mureytasroc/trintheremin-public/Circuit_Design/Design Pictures/Schematic/SchematicFull.jpg

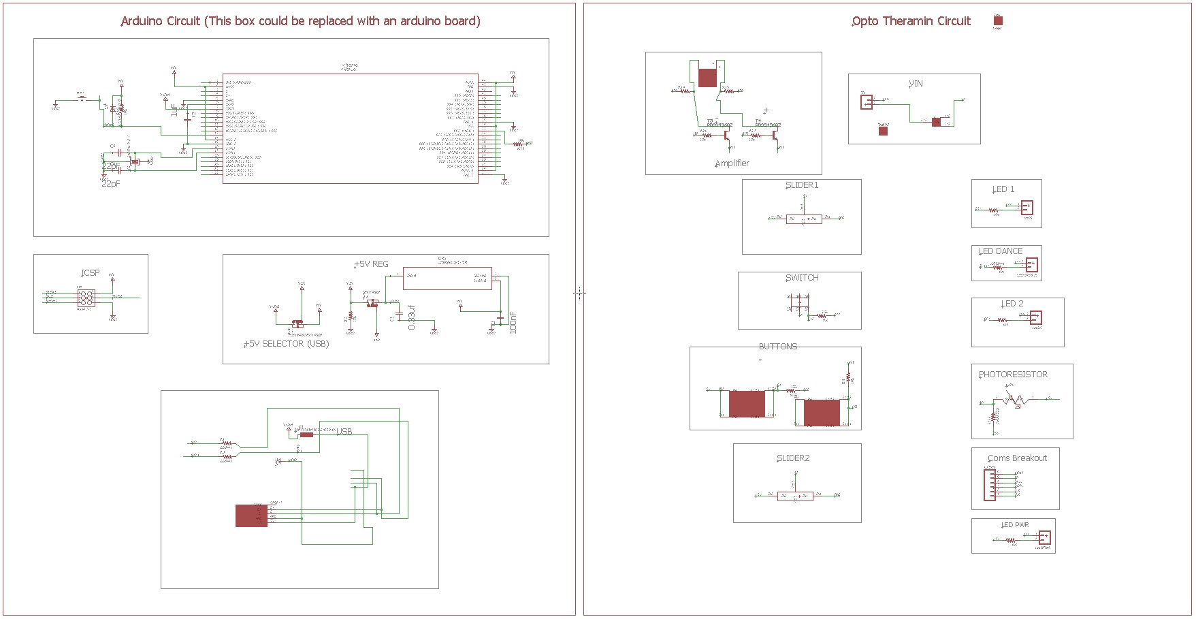
Circuit_Design/Design Pictures/Schematic/SchematicFull.jpg
