mureytasroc/trintheremin-public/TrinTheremin Resources/Circuit Design/TrinTheremin.sch

## EAGLE design TrinTheremin Resources/Circuit Design/TrinTheremin.sch (2017-09-11)


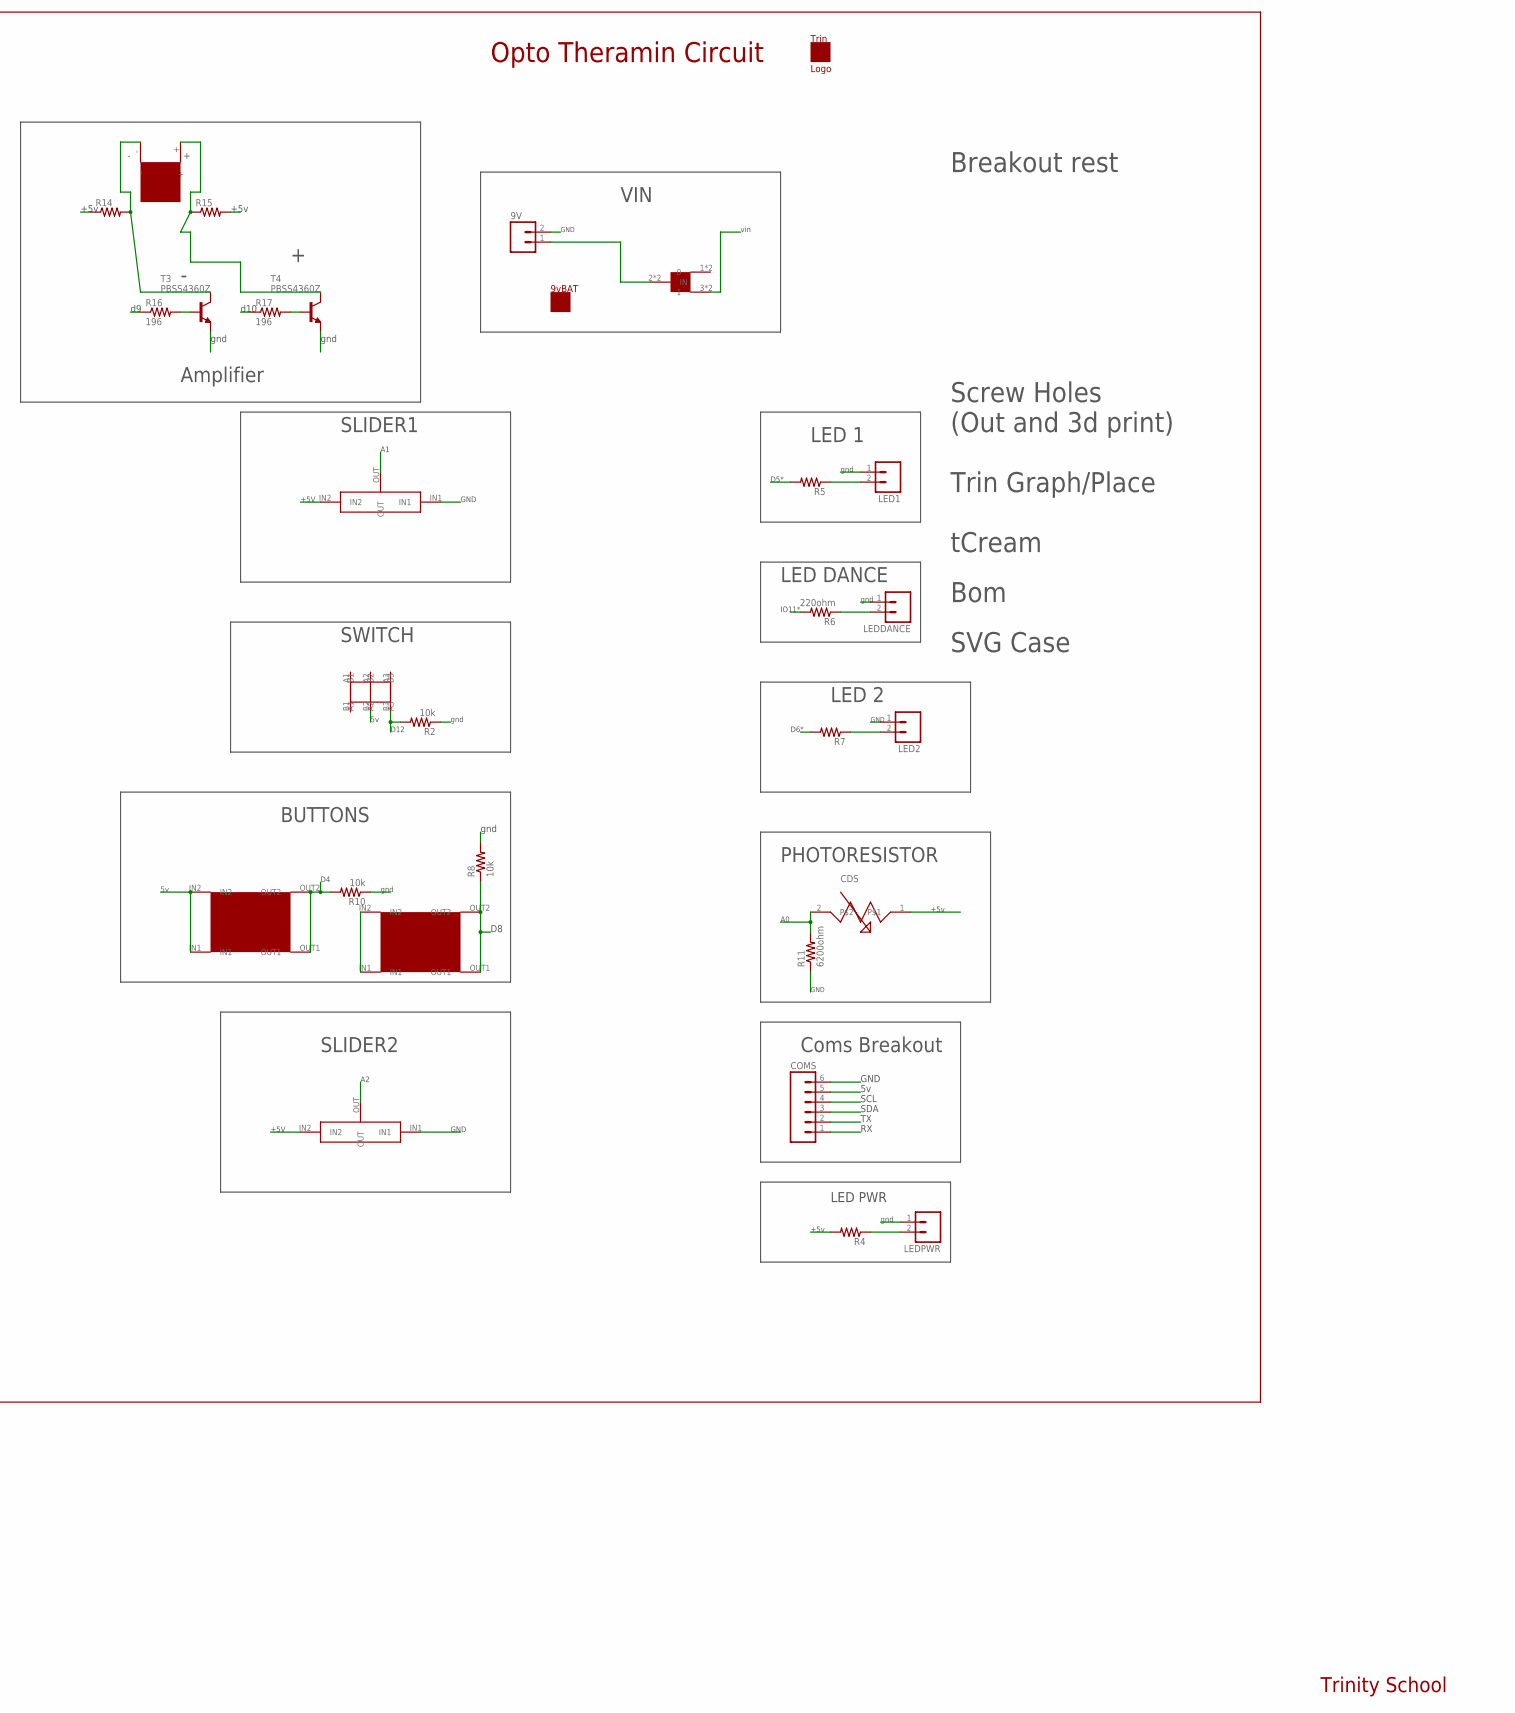
[picture p22: schematic TrinTheremin.sch, part in row 1, column 2]

Parts:
9V: M02PTH; 1X02
C1: 0.33uf; CAPC2013X110N
C2: 100nF; CAPC2013X110N
C3: 1uF; CAPC1608X85N
C4, C5: 22pF; CAPC1608X85N
COMS: M06SILK_FEMALE_PTH; 1X06
CR1: L7805CDT-TR; DPAK
D1: CD1206-S01575; MINIMELF
F1: MF-MSMF050-2 500mA; L1812
ICSP: FEMALE 2x3; 2X3
LED1, LED2: M02PTH; 1X02
LEDDANCE: M02PTH; 1X02
LEDPWR: M02PTH; 1X02
R1, R3: 22ohm; R0603
R2, R8, R9, R10, R12, R13: 10k; 0603-RES
R4, R5, R7: RESISTOR0603; 0603-RES
R6: 220ohm; 0603-RES
R11: 6200ohm; 0603-RES
R14, R15: R-US_R2512; R2512
R16, R17: 196; 1206
RESET: SWITCH_PUSHBUTTONC&K_KSS; BTN_CK_KSS
T1: FDN340P/PMV48XP; SOT-23
T2: PMV48XP; SOT-23
T3, T4: PBSS4360Z; SOT223
U$3: ATMEGA32U4-AU; 44ML
U$8: PWRSWITCHTHRU
U$9: CDS
U$10, U$14: DIGISLIDER
U$11: DIGISWITCH
U$13, U$17: BUT97
U$15: 9VBATHOLDERTALL
U$16: TRIN
U$20: GOODSPEAKER
U$23: MICROUSB
Y2: 16MHz KX-7; CRYSTAL-3.2-2.5

Connections:
+5V: C2.2 (C2), COMS.5, CR1.2 (OUTPUT), D1.C, ICSP.2, R4.2, R12.2, R14.1, R15.2, T1.2 (S), T2.3 (G), U$3.2 (UVCC), U$3.14 (VCC_2), U$3.24 (AVCC_2), U$3.34 (VCC), U$3.44 (AVCC), U$9.1, U$10.IN2, U$11.B2, U$13.IN1, U$13.IN2, U$14.IN2, U$17.IN1, U$17.IN2
+VIN: C1.2 (C2), CR1.1 (INPUT), T2.2 (S)
A0: R11.2, U$3.36 (PF7_(ADC7/TDI)), U$9.2
A1: U$3.37 (PF6_(ADC6/TDO)), U$10.OUT
A2: U$3.38 (PF5_(ADC5/TMS)), U$14.OUT
A3: U$3.39 (PF4_(ADC4/TCK))
A4: U$3.40 (PF1_(ADC1))
A5: U$3.41 (PF0_(ADC0))
BASE: R16.2, T3.1 (B)
COL: R14.2, T3.2 (C), U$20.-
D0/RX: COMS.1, U$3.20 ((RXD1/INT2)_PD2)
D1/TX: COMS.2, U$3.21 ((TXD1/INT3)_PD3)
D2/SDA: COMS.3, U$3.19 ((SDA/INT1)_PD1)
D3/SCL: COMS.4, U$3.18 ((OC0B/SCL/INT0)_PD0)
D4*: R10.2, U$3.25 (PD4_(ICP1/ADC8), U$13.OUT1, U$13.OUT2
D5*: R5.2, U$3.31 (PC6_(OC3A/OC4A!))
D6*: R7.2, U$3.27 (PD7_(T0/OC4D/ADC10))
D7: U$3.1 (INT.6/AIN0)PE6)
D+: R3.2, U$23.D+
D-: R1.2, U$23.D-
GND: 9V.2, C1.1 (C1), C2.1 (C1), C3.2 (C2), C4.1 (C1), C5.1 (C1), COMS.6, CR1.3 (GROUND), ICSP.6, LED1.1, LED2.1, LEDDANCE.1, LEDPWR.1, R2.1, R8.2, R9.1, R10.1, R11.1, R13.1, RESET.P$1, T3.3 (E), T4.3 (E), U$3.5 (UGND), U$3.15 (GND_2), U$3.23 (GND_3), U$3.35 (GND_4), U$3.43 (GND), U$10.IN1, U$14.IN1, U$23.GND, Y2.2 (GND), Y2.4 (GND)
HWB: R13.2, U$3.33 (PE2_(HWB!))
IO8: R8.1, U$3.28 (PB4_(PCINT4/ADC11)), U$17.OUT1, U$17.OUT2
IO9*: R16.1, U$3.29 (PB5_(PCINT5/OC1A/OC4B/ADC12))
IO10*: R17.1, U$3.30 (PB6_(PCINT6/OC1B/OC4B/ADC13))
IO11*: R6.2, U$3.12 ((PCINT7/OC0A/OC1C/RTS!)_PB7)
IO12*: R2.2, U$3.26 (PD6_(T1/OC4D/ADC9)), U$11.B3
IO13*: U$3.32 (PC7_(ICP3/CLK0/OC4A))
MISO: ICSP.1, U$3.11 ((PDO/PCINT3/MISO)_PB3)
MOSI: ICSP.4, U$3.10 ((PDI/PCINT2/MOSI)_PB2)
unnamed: LED1.2, R5.1
unnamed: R17.2, T4.1 (B)
unnamed: C3.1 (C1), U$3.6 (UCAP)
unnamed: R15.1, T4.2 (C), U$20.+
unnamed: LEDDANCE.2, R6.1
unnamed: LED2.2, R7.1
unnamed: 9V.1, U$8.2 (IN)
unnamed: LEDPWR.2, R4.1
RAWUSB: F1.1, U$23.5V
RD+: R3.1, U$3.4 (D+)
RD-: R1.1, U$3.3 (D-)
RESET: D1.A, ICSP.5, R12.1, RESET.P$2, U$3.13 (!)
RXLED/SS: U$3.8 ((SS/PCINT0)_PB0)
SCK: ICSP.3, U$3.9 ((PCINT1/SCLK)_PB1)
TXLED: U$3.22 ((XCK1/CTS!)_PD5)
VIN: R9.2, T1.3 (G), T2.1 (D), U$8.3 (1)
VUSB: F1.2, T1.1 (D), U$3.7 (VBUS)
XTAL3: C4.2 (C2), U$3.16 (XTAL2), Y2.1 (C1)
XTAL4: C5.2 (C2), U$3.17 (XTAL1), Y2.3 (C2)

Notes on the sheet:
+5V REG
ICSP
USB
+5V SELECTOR (USB)
CDS
GND
gnd
Arduino Circuit (This box could be replaced with an arduino board)
Opto Theramin Circuit
Trinity School
LED 2
LED DANCE
Coms Breakout
PHOTORESISTOR
LED 1
+5v
VIN
SWITCH
BUTTONS
SLIDER1
SLIDER2
vin
+5V
LED PWR
D5*
D6*
IO11*
D12
Breakout rest
Screw Holes (Out and 3d print)
Trin Graph/Place
tCream
Bom
SVG Case
Amplifier
d10
SDA
SCL
